MohamedAliRashad/ASUMobiCarG36/Control/PCB Prototype V1.bmp

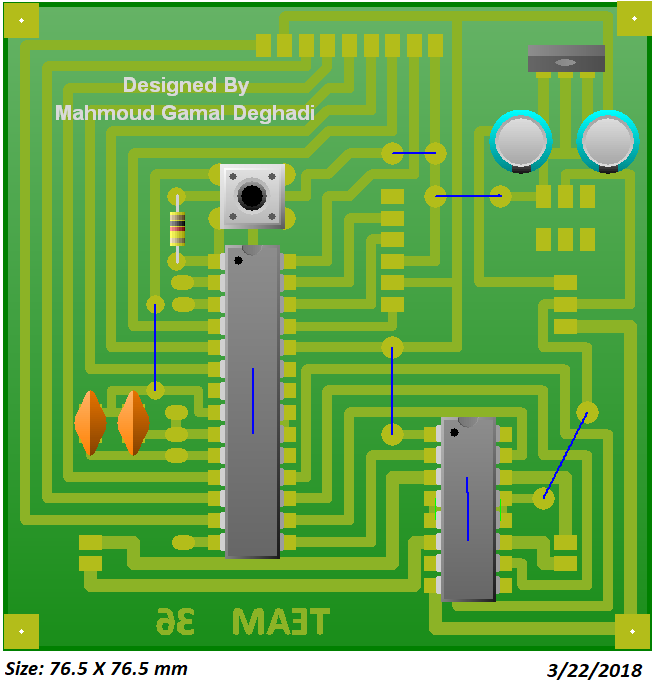
Control/PCB Prototype V1.bmp
