MohamedAliRashad/ASUMobiCarG36/Control/PCB Version 2.bmp

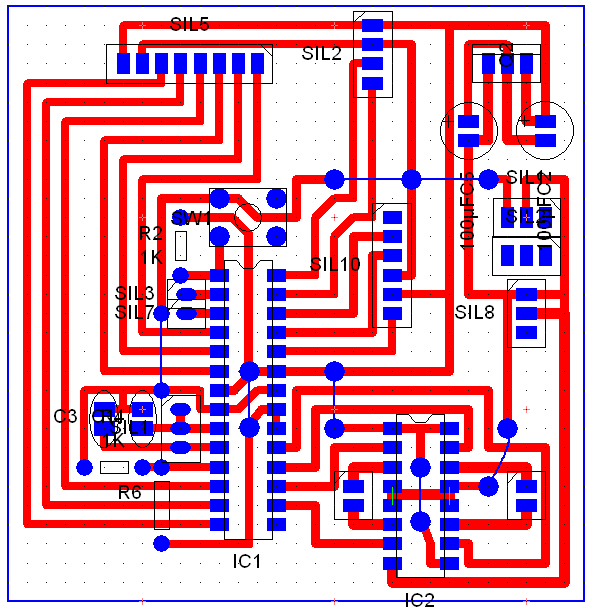
Control/PCB Version 2.bmp
