MohamedAliRashad/ASUMobiCarG36/Control/Snap of design the App.png

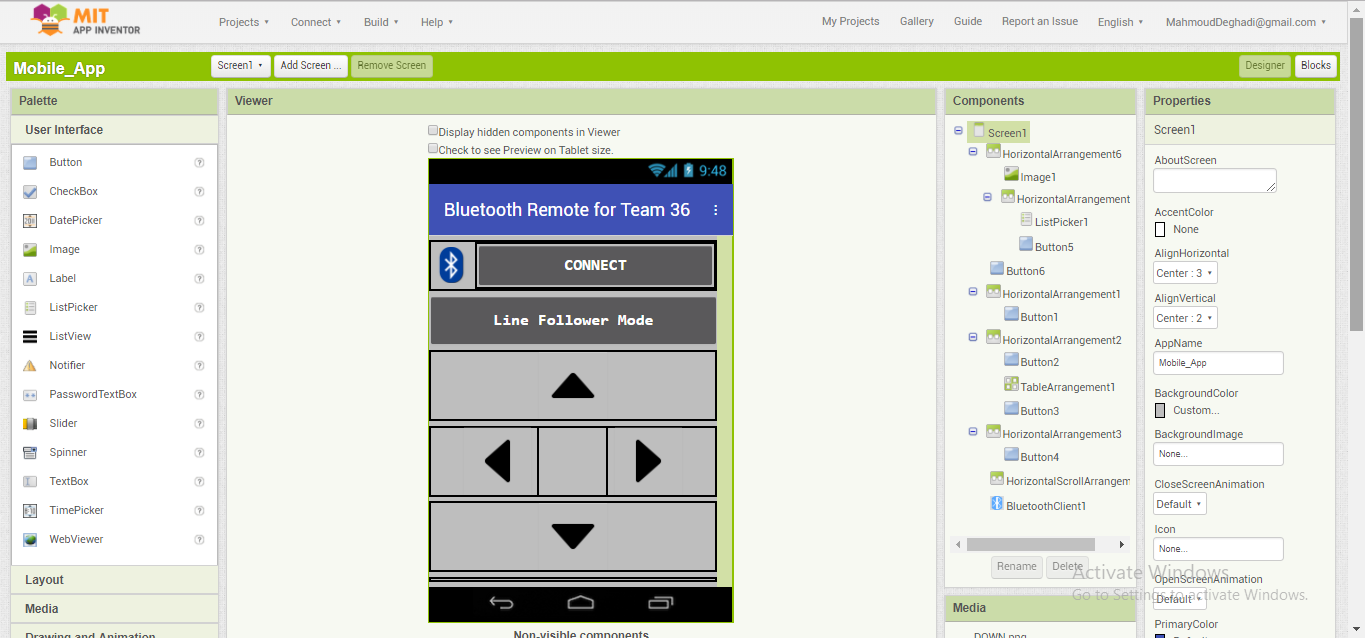
Control/Snap of design the App.png
