MohamedAliRashad/ASUMobiCarG36/Control/Snap of PCB V1.jpg

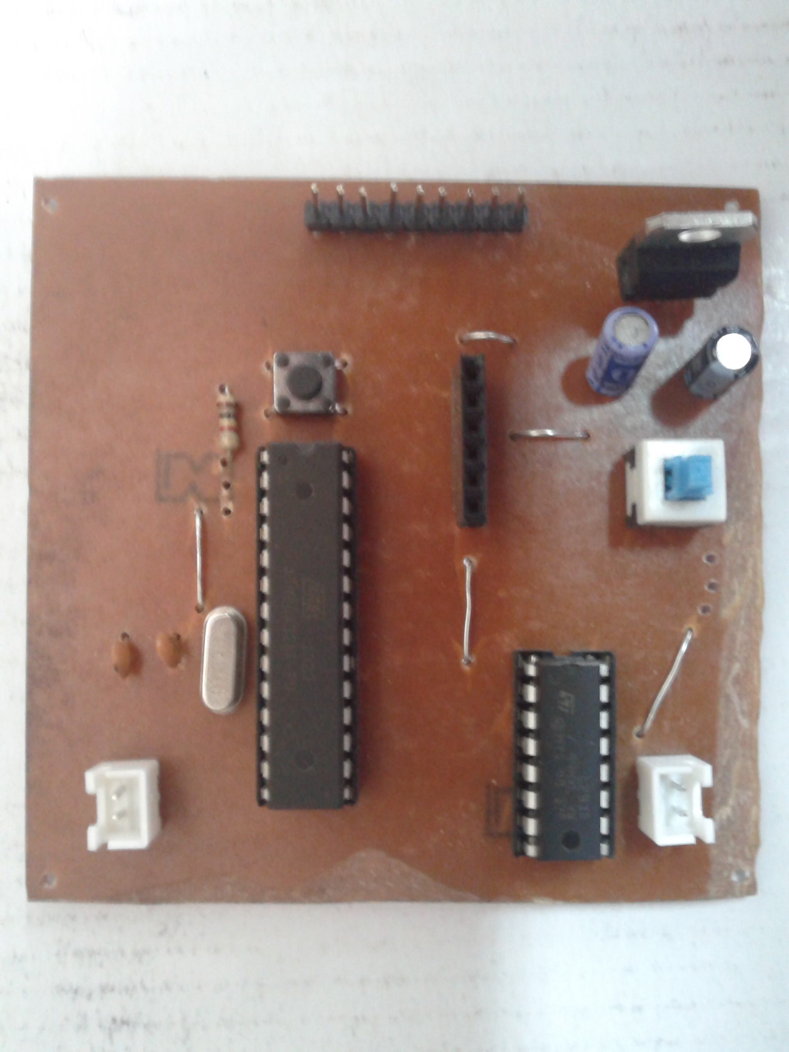
Control/Snap of PCB V1.jpg
