MohamedAliRashad/ASUMobiCarG36/Control/Snap of prototype 3_2_2018.jpg

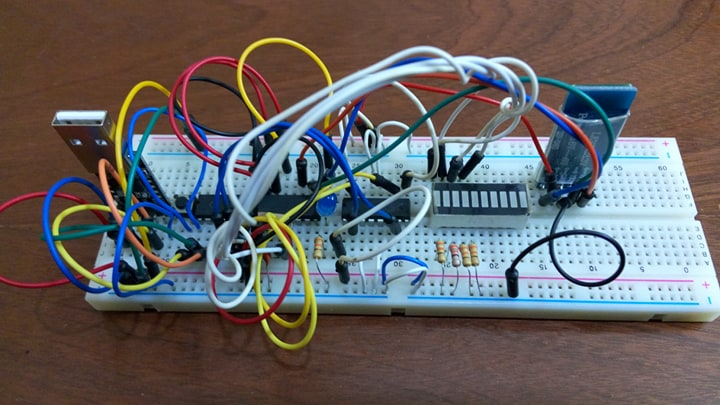
Control/Snap of prototype 3_2_2018.jpg
