MohamedAliRashad/ASUMobiCarG36/Designing/Car_V1.jpg

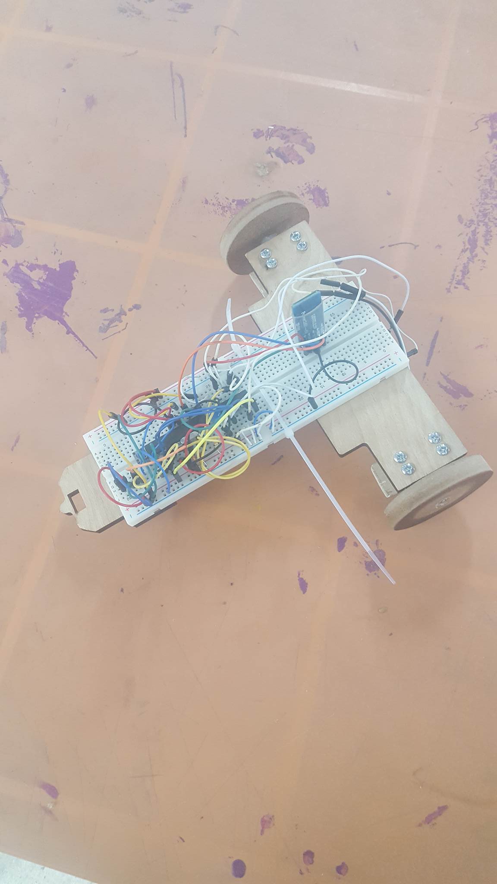
Designing/Car_V1.jpg
