MohamedAliRashad/ASUMobiCarG36/Designing/Chariot/images/cc96dc8cfa2f17d860a1af37f6951727_preview_featured.jpg

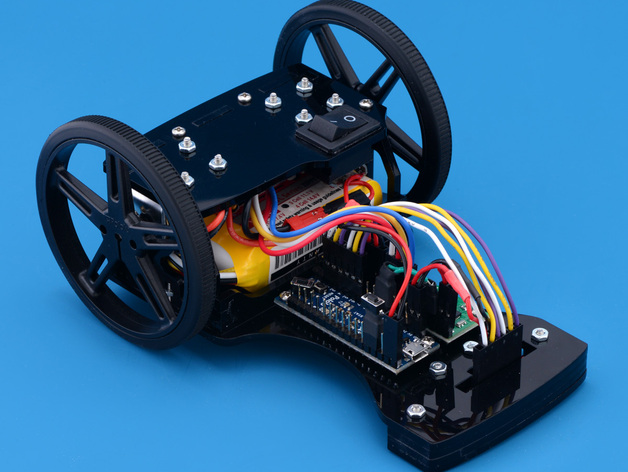
Designing/Chariot/images/cc96dc8cfa2f17d860a1af37f6951727_preview_featured.jpg
