MohamedAliRashad/ASUMobiCarG36/Designing/Chariot/images/d321be938b5083fad38181116606ea06_preview_featured.jpg

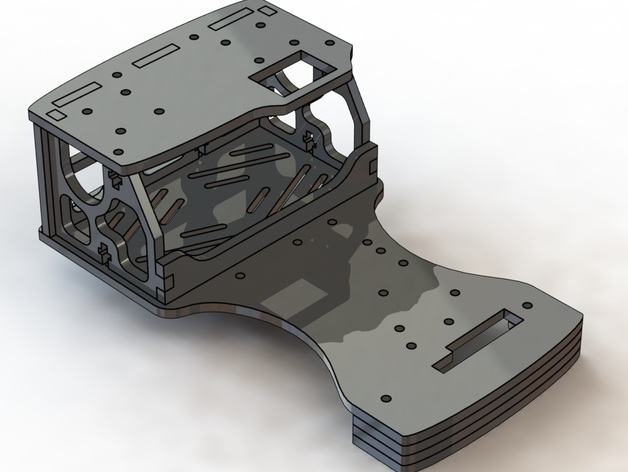
Designing/Chariot/images/d321be938b5083fad38181116606ea06_preview_featured.jpg
