MohamedAliRashad/ASUMobiCarG36/Designing/DSC_0131.JPG

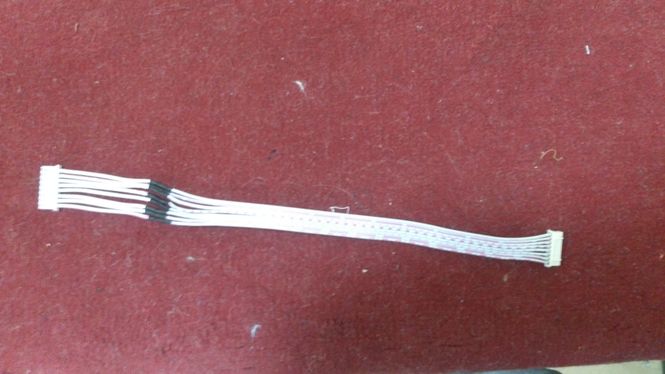
Designing/DSC_0131.JPG
