MohamedAliRashad/ASUMobiCarG36/Designing/DSC_0132.JPG

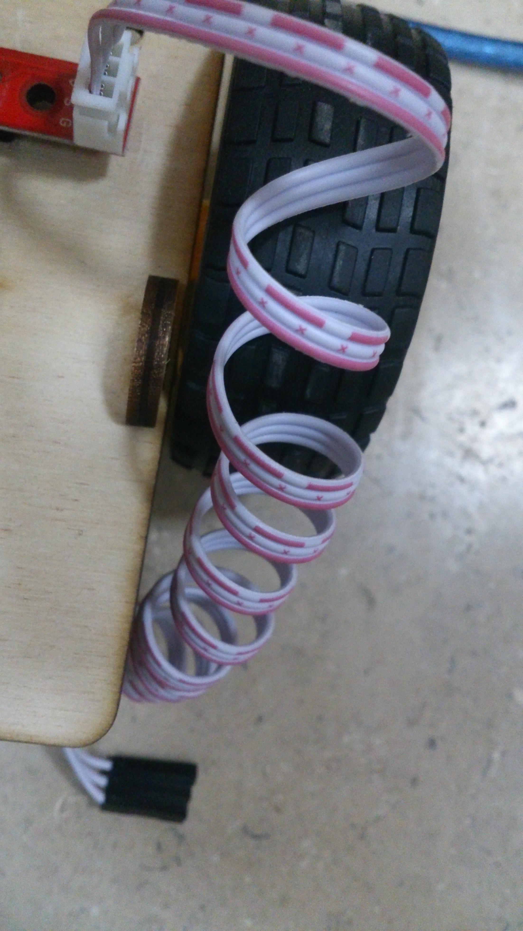
Designing/DSC_0132.JPG
