MohamedAliRashad/ASUMobiCarG36/Designing/DSC_0135.JPG

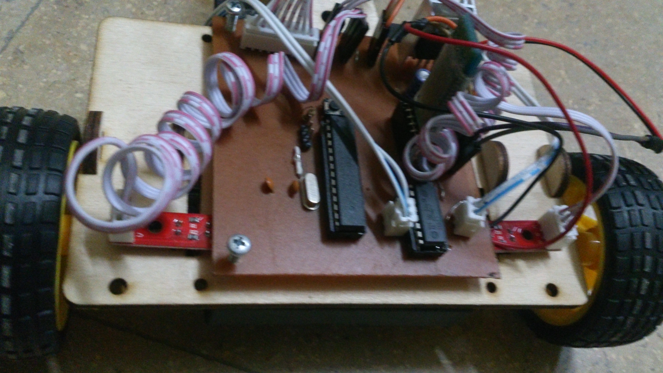
Designing/DSC_0135.JPG
