MohamedAliRashad/ASUMobiCarG36/Designing/DSC_0136.JPG

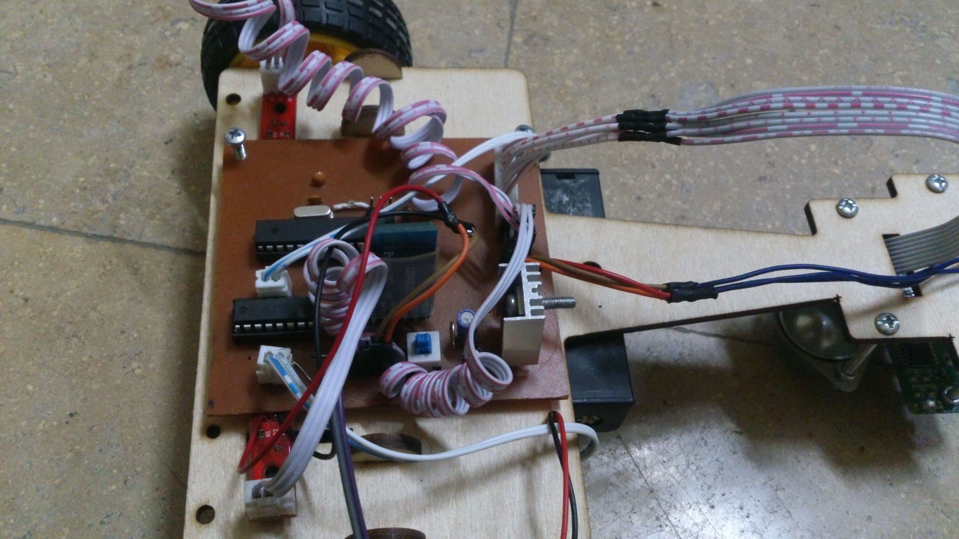
Designing/DSC_0136.JPG
