MohamedAliRashad/ASUMobiCarG36/Designing/Target/20180301_035607.jpg

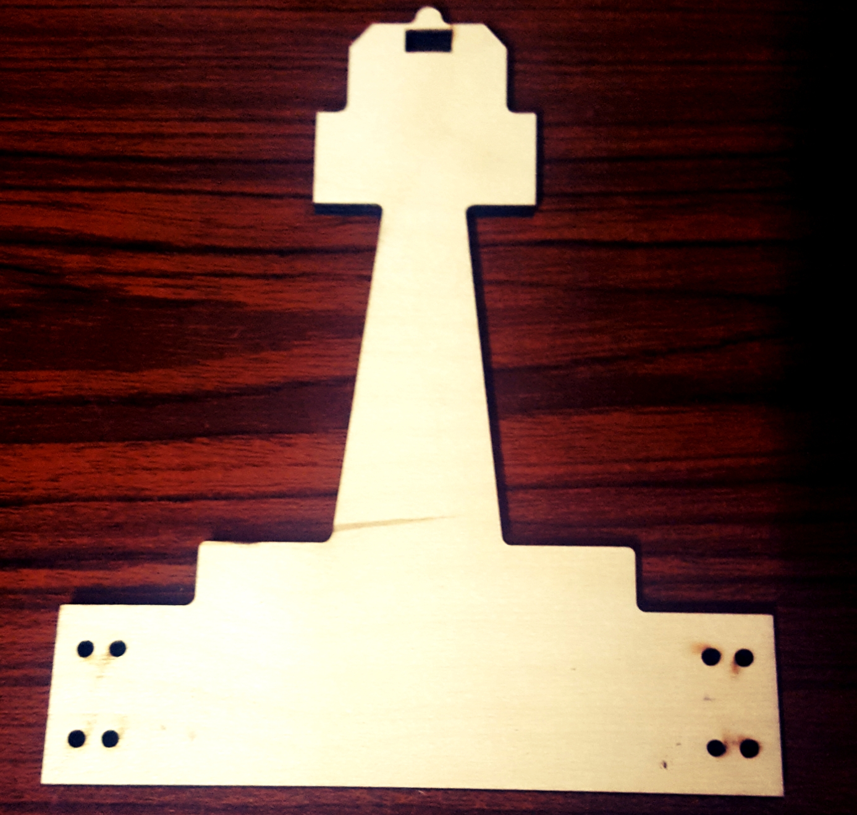
Designing/Target/20180301_035607.jpg
