MohamedAliRashad/ASUMobiCarG36/Designing/Target/images/5cac82019ea96a651d6817cba1ffc6b6_preview_featured.jpg

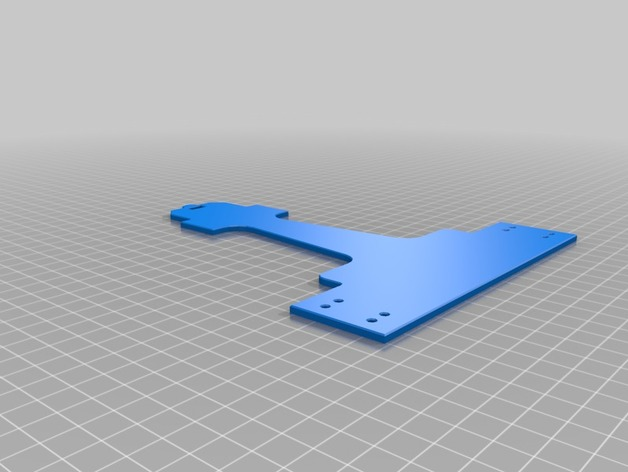
Designing/Target/images/5cac82019ea96a651d6817cba1ffc6b6_preview_featured.jpg
