MohamedAliRashad/ASUMobiCarG36/Designing/Target/images/48e5445a98966c84df6731cb48f92077_preview_featured.jpg

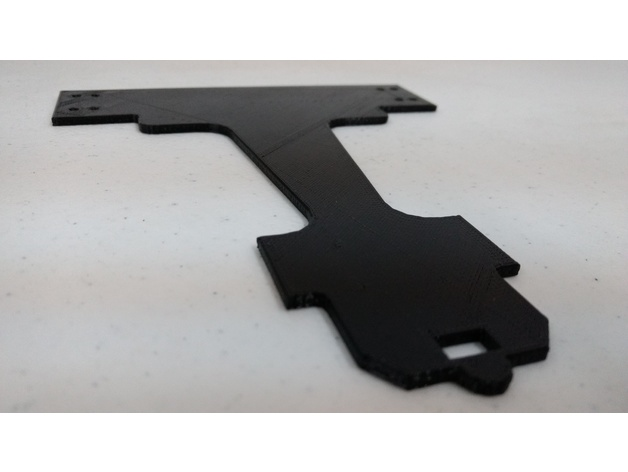
Designing/Target/images/48e5445a98966c84df6731cb48f92077_preview_featured.jpg
