MohamedAliRashad/ASUMobiCarG36/Designing/Target/images/069bf8baaa3e0a5343f99e9a37863103_preview_featured.jpg

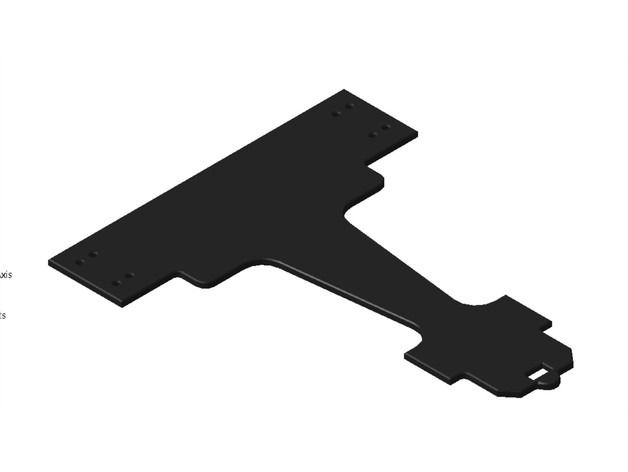
Designing/Target/images/069bf8baaa3e0a5343f99e9a37863103_preview_featured.jpg
