MohamedAliRashad/ASUMobiCarG36/Designing/Usain/images/8ac9102e7b1bd56f0f8071486dcb0fc8_preview_featured.jpg

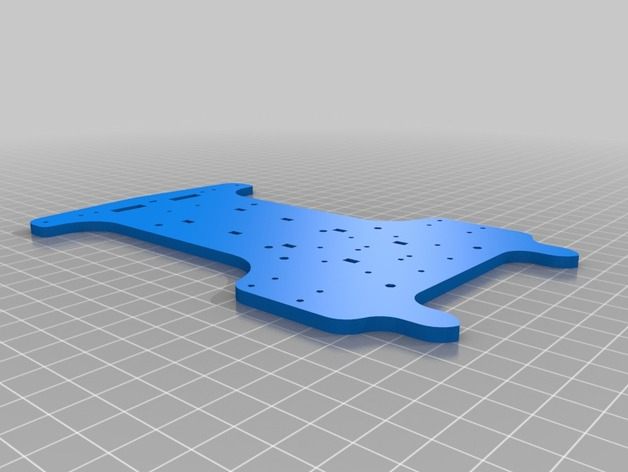
Designing/Usain/images/8ac9102e7b1bd56f0f8071486dcb0fc8_preview_featured.jpg
