MohamedAliRashad/ASUMobiCarG36/Designing/Usain/images/bottom_preview_featured.jpg

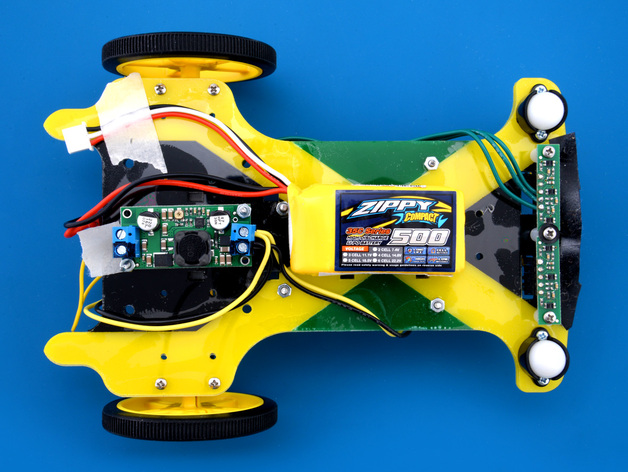
Designing/Usain/images/bottom_preview_featured.jpg
