MohamedAliRashad/ASUMobiCarG36/Designing/Usain/images/front_preview_featured.jpg

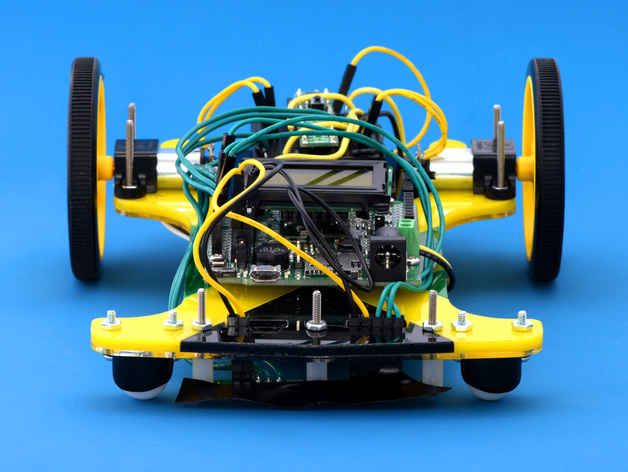
Designing/Usain/images/front_preview_featured.jpg
