MohamedAliRashad/ASUMobiCarG36/Designing/Usain/images/iso_preview_featured.jpg

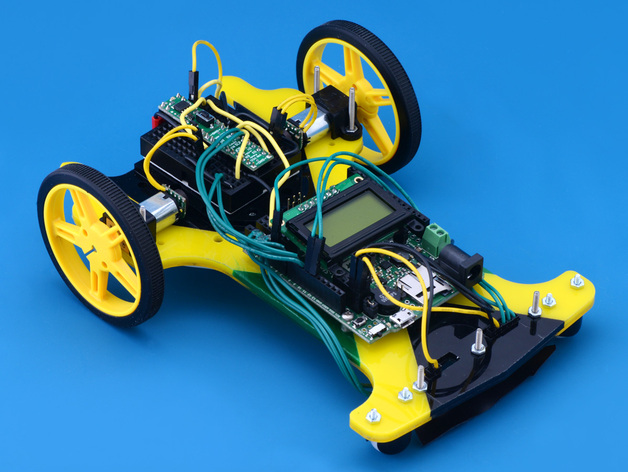
Designing/Usain/images/iso_preview_featured.jpg
