MohamedAliRashad/ASUMobiCarG36/Designing/Usain/images/side_preview_featured.jpg

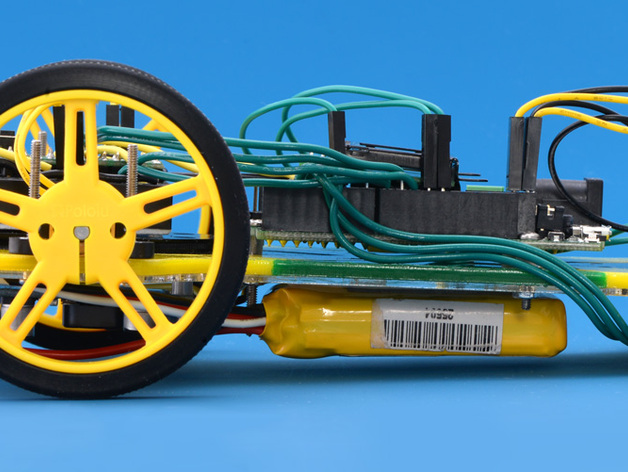
Designing/Usain/images/side_preview_featured.jpg
