MohamedAliRashad/ASUMobiCarG36/Designing/Usain/images/usain_volt_yellow_piece_preview_featured.jpg

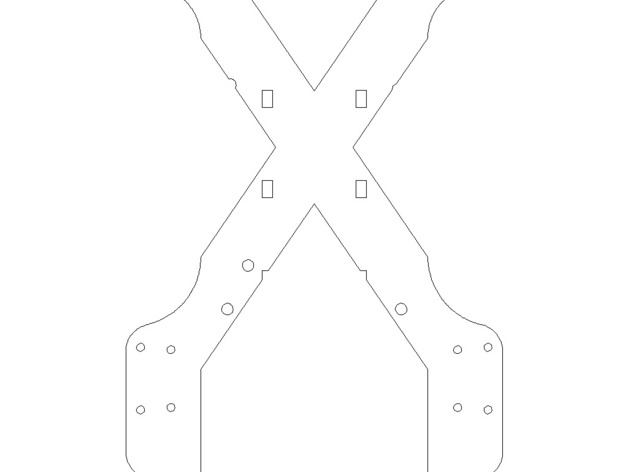
Designing/Usain/images/usain_volt_yellow_piece_preview_featured.jpg
