MohamedAliRashad/ASUMobiCarG36/Designing/Chariot/files/chariot-front-wall.STEP

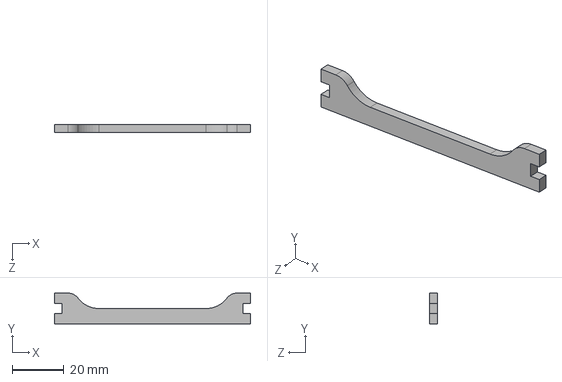
[picture p46: CAD file, 2018-02-19]
Designing/Chariot/files/chariot-front-wall.STEP
76.0 x 12.0 x 3.00 mm
