MohamedAliRashad/ASUMobiCarG36/Designing/Chariot/files/chariot-led-shroud.STEP

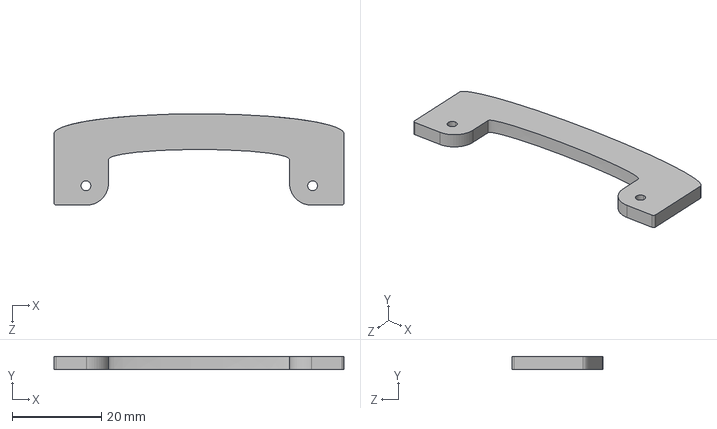
[picture p47: CAD file, 2018-02-19]
Designing/Chariot/files/chariot-led-shroud.STEP
65.0 x 3.00 x 20.5 mm
