MohamedAliRashad/ASUMobiCarG36/Designing/Chariot/files/chariot-back-wall.STEP

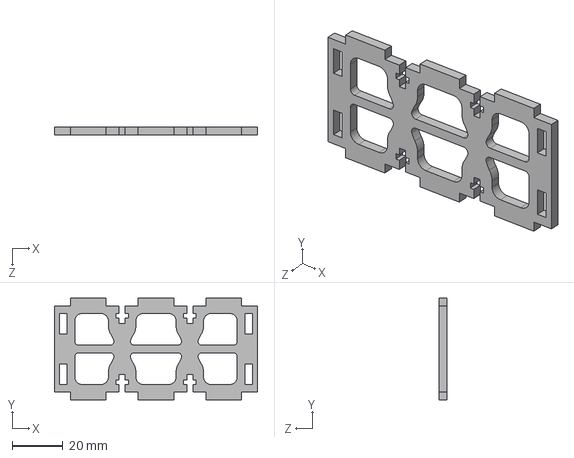
[picture p48: CAD file, 2018-02-19]
Designing/Chariot/files/chariot-back-wall.STEP
80.0 x 40.0 x 3.00 mm
